stuartpittaway/diyBMS-CurrentShunt/Code/diybmsCurrentShunt/buildscript.py

Import("env")

platform = env.PioPlatform()

#print(env.get("BOARD"))

if env.get("BOARD")=="ATtiny1614":
    #print(env)
    #print(platform)

    my_flags = env.ParseFlags(env['BUILD_FLAGS'])
    #print(my_flags)
    defines = {k: v for (k, v) in my_flags.get("CPPDEFINES")}
    #print(defines.get("DIYBMSMODULEVERSION"))

#    efuse=hex(int(env.GetProjectOption("board_fuses.efuse"), 2)).upper()[2:4]
#    hfuse=hex(int(env.GetProjectOption("board_fuses.hfuse"), 2)).upper()[2:4]
#    lfuse=hex(int(env.GetProjectOption("board_fuses.lfuse"), 2)).upper()[2:4]

    env.Replace(PROGNAME="%s_%s" % (env["PIOENV"],env.get("BOARD") ))
